Stephane-Peel/Typhoon-Rework/Typhoon-Kicad-3D-Renders & Exports/Typhoon-FrontPlateWorking-Kicad_v1_2026-Jan-17_02-12-00PM-000_CustomizedView3675384114.png

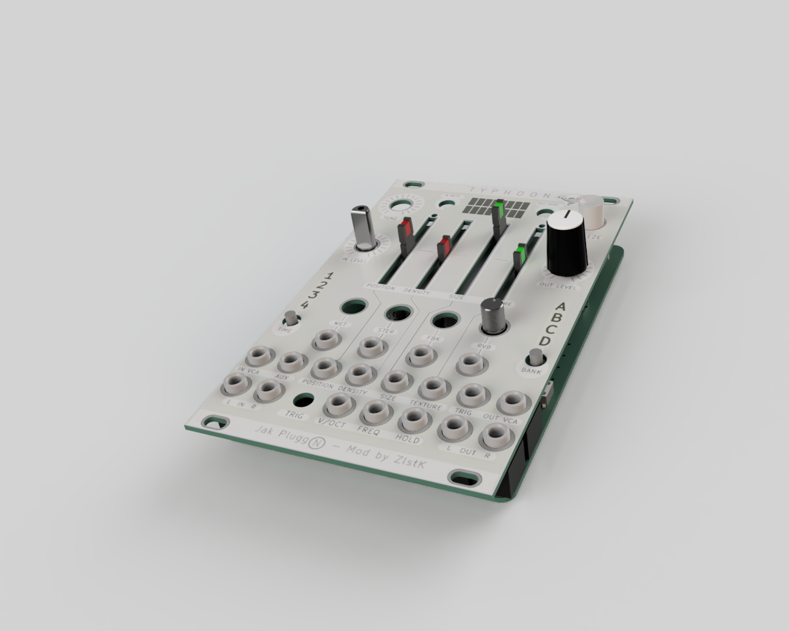
Typhoon-Kicad-3D-Renders & Exports/Typhoon-FrontPlateWorking-Kicad_v1_2026-Jan-17_02-12-00PM-000_CustomizedView3675384114.png
